GPXenergy/gpx_connector/gpx_connector/http_pages.cpp

#include <WebServer.h>
#include "http_pages.h"
#include "user_config.h"

#define TITLE_HOME "Home"
#define TITLE_UPDATE "Update firmware"
#define TITLE_STATUS "Status"
#define TITLE_CONF_DEVICE "Configure device"
#define TITLE_CONF_CONNECTION "Configure connection"

const char* success_message = "<p><em>Configurations saved!</em></p>";

const char* local_resources =
    "<link rel='stylesheet' href='/pure.css'>";

const char* online_resources =
    "<script src='https://ajax.googleapis.com/ajax/libs/jquery/3.2.1/jquery.min.js'></script>"
    "<link rel='stylesheet' href='https://use.fontawesome.com/releases/v5.8.2/css/all.css' "
    "integrity='sha384-oS3vJWv+0UjzBfQzYUhtDYW+Pj2yciDJxpsK1OYPAYjqT085Qq/1cq5FLXAZQ7Ay' crossorigin='anonymous'>";

const char* fallback_resources =
    "";

const char* update_firmware_script =
    "(e=>{const t=(...t)=>e.querySelector(...t),n=t('form'),a=t('#status');n.addEventListener('submit',e=>{e.prevent"
    "Default();const s=new FormData(n),o=t('#file').files[0],d=new XMLHttpRequest;o?(n.classList.add('uploading'),s."
    "append('update',o),d.addEventListener('load',e=>{a.innerText='Applying update...';setTimeout(()=>{a.innerText='"
    "Upload success! The device will restart to apply the update, you can change back to active mode afterwards.';co"
    "nst t=new XMLHttpRequest;t.open('get','/reboot'),t.send()},2000)}),d.addEventListener('error',e=>{a.innerText='"
    "Upload failed... Try again or contact help@gpx.nl',n.classList.remove('uploading')}),d.addEventListener('abort'"
    ",e=>{a.innerText='Upload cancelled...'}),d.upload.addEventListener('progress',e=>{if(e.lengthComputable){a.inne"
    "rText='Uploading new firmware... This can take up to 10 minutes.';const n=Math.round(e.loaded/e.total*100)+'%';"
    "t('#prg').innerText=n,t('#bar').style.width=n}}),d.open(n.method,n.action),d.send(s)):a.innerText='Please selec"
    "t a file...'})})(this.document);";

/**
 * page format
 * %s - page name (page title)
 * %d - device id (page title)
 * %s - remote resources
 * %s - local resources
 * %d - device id (menu title)
 * %s - page content (main content)
 */
const char* base_page_format_begin =
    "<!DOCTYPE html>"
    "<html lang='en'><head>"
    "<meta name='viewport' content='width=device-width, initial-scale=1.0'>"
    "<title>%s | GPX-Connector</title>"
    "%s"
    "%s"
    "<style>"
    "i{width: 25px;text-align: center;}"
    ".pure-form-message{font-style: italic;margin-bottom: 12px;}"
    "#layout{max-width: 680px;margin: auto;}"
    "#main{padding:1em;}"
    "input[type='text'],input[type='number']{max-width: 300px;width: 100%%;}"
    ".pure-menu-link{padding: 1em .7em;}"
    "</style>"
    "</head>"
    "<body>"
    "<div id='layout'>"
    "<div id='header'>"
    "<div class='pure-menu pure-menu-horizontal'>"
    "<a href='/' class='pure-menu-heading'>GPX-Connector</a>"
    "<ul class='pure-menu-list'>"
    "<li class='pure-menu-item pure-menu-has-children pure-menu-allow-hover'>"
    "<a href='#' id='menuLink1' class='pure-menu-link'><i class='fa fa-cog'></i>Configure</a>"
    "<ul class='pure-menu-children'>"
    "<li class='pure-menu-item'><a href='/device' class='pure-menu-link'><i class='fa fa-tablet'></i>Device</a></li>"
    "<li class='pure-menu-item'><a href='/connection' class='pure-menu-link'><i class='fa fa-wifi'></i>Connection</a></li>"
    "</ul></li>"
    "<li class='pure-menu-item'><a href='/update' class='pure-menu-link'><i class='fa fa-download'></i>Update firmware</a></li>"
    "<!--<li class='pure-menu-item'><a href='/status' class='pure-menu-link'><i class='fas fa-info-circle'></i>Status</a></li>-->"  // TODO: comment this out once status page is done
    "<li class='pure-menu-item'><a target='_blank' href='https://github.com/GPXenergy/gpx_connector' class='pure-menu-link'><i class='fab fa-github'></i>Github</a></li>"
    "</ul>"
    "</div>"
    "</div>"
    "<script>"
    "document.querySelectorAll('.pure-menu-item').forEach((e)=>e.children[0].href===window.location.href?e.classList.add('pure-menu-selected'):0);"
    "</script>"
    "<div id='main'>";

const char* base_page_format_end =
    "</div>"
    "</div>"
    "</body></html>";

const char* HttpPages::get_home_page() {
  return render_full_page(
      TITLE_HOME,
      "<h1>Manage your GPX-Connector</h1>"
      "<p class='pure-form-message'>GPX-Connector version %s</p>"
      "<p>"
      "<ul>"
      "<li><a href='/device'>Configure your device</a></li>"
      "<li><a href='/connection'>Configure your connection to the API</a></li>"
      "<li><a href='/update'>Update the firmware</a></li>"
      "</ul>"
      "More information about configurations in the <a href='dashboard.gpx.nl/manual' target='_blank'>User manual</a>."
      "</p>",
      GPX_CONN_VERSION
  );
}

const char* HttpPages::get_update_page() {
  return render_full_page(
      TITLE_UPDATE,
      "<div id='update'>"
      "<form class='pure-form pure-form-stacked' method='POST' enctype='multipart/form-data'>"
      "<fieldset>"
      "<legend><a href='/'>Home</a> / Update the firmware</legend>"
      "<div id='upload-inputs'>"
      "<p><em>Current version: v" GPX_CONN_VERSION "</em></p>"
      "<input type='file' name='update' id='file'><br>"
      "<span class='pure-form-message'>The latest firmware can be downloaded from <a target='_blank' href='https://github.com/GPXenergy/gpx_connector'>Github</a>. "
      "</span>"
      ""
      "<br>"
      "<input type='submit' class='pure-button pure-button-primary' value='Upload'>"
      "</div>"
      "<p id='status'></p>"
      "<div id='upload-progress'>"
      "<div style='background:#eee'><div id='bar' style='background:#ccc;height:10px'></div></div>"
      "<div id='prg' style='text-align:center'></div>"
      "</div>"
      "</fieldset>"
      "</form>"
      "<script>"
      "%s"
      "</script>"
      "<style>"
      "#upload-progress{display:none}"
      "form.uploading #upload-inputs{display:none}"
      "form.uploading #upload-progress{display:block}"
      "</style>"
      "</div>",
      update_firmware_script
  );
}

const char* HttpPages::get_config_device_page(
    bool display_success,
    const char* device_ssid,
    const char* device_password,
    uint32_t meter_conn_baud,
    uint16_t meter_conn_parity,
    bool inverter_enabled,
    uint8_t current_sensor_amps,
    uint8_t phase_type
) {
  return render_full_page(
      TITLE_CONF_DEVICE,
      "<form class='pure-form pure-form-stacked' action='/save?next=/device' method='POST'>"
      "<fieldset>"
      "<legend><a href='/'>Home</a> / Device settings</legend>"

      // GPX-Connector access point ssid
      "<label for='" FORM_NAME_AP_SSID "'>GPX-Connector wifi name</label>"
      "<input type='text' name='" FORM_NAME_AP_SSID "' id='" FORM_NAME_AP_SSID "' value='%s'>"
      "<span class='pure-form-message'>"
      "Network name for connecting to the configuration server"
      "</span>"

      // GPX-Connector access point password
      "<label for='" FORM_NAME_AP_PASS "'>GPX-Connector wifi password</label>"
      "<input type='text' name='" FORM_NAME_AP_PASS "' id='" FORM_NAME_AP_PASS "' value='%s'>"
      "<span class='pure-form-message'>"
      "Password for the configuration WiFi network (either empty or at least 8 characters long)"
      "</span>"

      "<h2>Smart meter settings</h2>"

      // GPX-Connector meter connection baud rate
      "<label for='" FORM_NAME_METER_BAUD "'>Smart meter baud rate</label>"
      "<select name='" FORM_NAME_METER_BAUD "' id='" FORM_NAME_METER_BAUD "'>"
      "<option %s value='9600'>9600</option>"
      "<option %s value='115200'>115200</option>"
      "</select>"
      "<span class='pure-form-message'>"
      "See user manual for more information."
      "</span>"

      // GPX-Connector meter connection parity
      "<label for='" FORM_NAME_METER_PARITY "'>Smart meter parity</label>"
      "<select name='" FORM_NAME_METER_PARITY "' id='" FORM_NAME_METER_PARITY "'>"
      "<option %s value='0'>7E1</option>"
      "<option %s value='1'>8N1</option>"
      "</select>"
      "<span class='pure-form-message'>"
      "See user manual for more information."
      "</span>"

      "<h2>Solar Inverter settings</h2>"

      // GPX-Connector inverter connection enabled
      "<label>Connection</label>"
      "<label for='" FORM_NAME_INVERTER_ENABLED "0' class='pure-radio'>"
      "<input id='" FORM_NAME_INVERTER_ENABLED "0' type='radio' name='" FORM_NAME_INVERTER_ENABLED "' value='0' %s>No solar inverter connected"
      "</label>"
      "<label for='" FORM_NAME_INVERTER_ENABLED "1' class='pure-radio'>"
      "<input id='" FORM_NAME_INVERTER_ENABLED "1' type='radio' name='" FORM_NAME_INVERTER_ENABLED "' value='1' %s>Connected through current sensor"
      "</label>"
      "<span class='pure-form-message'>"
      "Solar inverter is not fully supported yet, enable at own risk."
      "</span>"

      // GPX-Connector current sensor type
      "<label for='" FORM_NAME_CURRENT_SENSOR_AMPS "'>Current sensor amps per 1v</label>"
      "<select name='" FORM_NAME_CURRENT_SENSOR_AMPS "' id='" FORM_NAME_CURRENT_SENSOR_AMPS "'>"
      "<option %s value='30'>30A/1v</option>"
      "<option %s value='50'>50A/1v</option>"
      "</select>"
      "<span class='pure-form-message'>"
      "See user manual for more information."
      "</span>"

      // GPX-Connector phase type
      "<label for='" FORM_NAME_PHASE_TYPE "'>Phase type (where current sensor is connected)</label>"
      "<select name='" FORM_NAME_PHASE_TYPE "' id='" FORM_NAME_PHASE_TYPE "'>"
      "<option %s value='1'>1-phase power</option>"
      "<option %s value='3'>3-phase power</option>"
      "</select>"
      "<span class='pure-form-message'>"
      "See user manual for more information."
      "</span>"

      "<br>"
      "<button type='submit' class='pure-button pure-button-primary'>Save</button>"
      "</fieldset>"
      "</form>"
      "%s", // Success message
      device_ssid,
      device_password,
      meter_conn_baud == 9800 ? "selected" : "",
      meter_conn_baud == 115200 ? "selected" : "",
      meter_conn_parity == MeterParity::e_meter_parity_7E1 ? "selected" : "",
      meter_conn_parity == MeterParity::e_meter_parity_8N1 ? "selected" : "",
      inverter_enabled ? "" : "checked",
      inverter_enabled ? "checked" : "",
      current_sensor_amps == 30 ? "selected" : "",
      current_sensor_amps == 50 ? "selected" : "",
      phase_type == 1 ? "selected" : "",
      phase_type == 3 ? "selected" : "",
      display_success ? success_message : ""
  );
}

const char* HttpPages::get_config_connection_page(
    bool display_success,
    const char* wifi_ssid,
    const char* wifi_password,
    const char* api_key,
    bool use_dev
) {
  return render_full_page(
      TITLE_CONF_CONNECTION,
      "<form class='pure-form pure-form-stacked' action='/save?next=/connection' method='POST'>"
      "<fieldset>"
      "<legend><a href='/'>Home</a> / Connection settings</legend>"

      // WiFi ssid
      "<label for='" FORM_NAME_WIFI_SSID "'>WiFi network name</label>"
      "<input type='text' name='" FORM_NAME_WIFI_SSID "' id='" FORM_NAME_WIFI_SSID "' value='%s'>"
      "<span class='pure-form-message'>Your home WiFi network name</span>"

      // WiFi password
      "<label for='" FORM_NAME_WIFI_PASS "'>WiFi password</label>"
      "<input type='text' name='" FORM_NAME_WIFI_PASS "' id='" FORM_NAME_WIFI_PASS "' value='%s'>"
      "<span class='pure-form-message'>Your home WiFi network password</span>"

      // Api key
      "<label for='" FORM_NAME_API_KEY "'>API key</label>"
      "<input type='text' name='" FORM_NAME_API_KEY "' id='" FORM_NAME_API_KEY "' value='%s'>"
      "<span class='pure-form-message'>"
      "Get your API key from <a target='_blank' href='https://dashboard.gpx.nl/configure/meter'>dashboard.gpx.nl</a><br>"
      "</span>"

      // Use dev
      "<label>Server</label>"
      "<label for='" FORM_NAME_USE_DEV "0' class='pure-radio'>"
      "<input id='" FORM_NAME_USE_DEV "0' type='radio' name='" FORM_NAME_USE_DEV "' value='0' %s>Standard"
      "</label>"
      "<label for='" FORM_NAME_USE_DEV "1' class='pure-radio'>"
      "<input id='" FORM_NAME_USE_DEV "1' type='radio' name='" FORM_NAME_USE_DEV "' value='1' %s>Development"
      "</label>"
      "<span class='pure-form-message'>"
      "Use development for testing and development purposes, the development server will not store data."
      "</span>"

      "<br>"
      "<button type='submit' class='pure-button pure-button-primary'>Save</button>"
      "</fieldset>"
      "</form>"
      "%s",
      wifi_ssid,
      wifi_password,
      api_key,
      use_dev ? "" : "checked",
      use_dev ? "checked" : "",
      display_success ? success_message : ""
  );
}

const char* HttpPages::get_status_page() {
  return render_full_page(
      TITLE_STATUS,
      "<form class='pure-form'>"
      "<fieldset>"
      "<legend><a href='/'>Home</a> / Status</legend>"
      "<pre style='background-color:#eee;padding:5px;font-size:12px;max-width:680px'>"
      "GPX version %s [%s]<br>"
      " - Current mode: %s<br>"
      "Meter data [%s]<br>"
      " - Last data: %s<br>"
      " - Valid: %s<br>"
      "Configuration server [%s]<br>"
      " - Status: %s<br>"
      "Api connection [%s]<br>"
      " - Status: %s<br>"
      "Server connection<br>"
      " - Status: %s (%d)<br>"
      "</pre>"
      "</fieldset>"
      "</form>",
      GPX_CONN_VERSION,
      "Active", // System state
      "Fixed", // - System mode
      "Active", // status
      "...", // - meter data
      "...", // - meter datavalid
      "Active", // Server state
      "Connected with wifi", // - Server status
      "Active", // Api state
      "Data posted", // - Api status
      "OK",   // - Server status
      200
  );
}

const char* HttpPages::render_full_page(const char* page_name, const char* content_format, ...) {
  sprintf(
      transmission_buffer,
      base_page_format_begin,
      page_name,
      local_resources,
      internet_access ? online_resources : fallback_resources
  );

  va_list args;
  va_start(args, content_format);
  vsprintf(
      &transmission_buffer[strlen(transmission_buffer)],
      content_format,
      args
  );
  va_end(args);

  sprintf(
      &transmission_buffer[strlen(transmission_buffer)],
      base_page_format_end
  );

  return transmission_buffer;
}

char HttpPages::transmission_buffer[] = "";

const char* HttpPages::pure_js =
    "(function (w,d){const a='active',l=d.getElementById('layout'),m=d.getElementById('menu'),n=d"
    ".getElementById('menuLink'),c=d.getElementById('main'),tc=(e,b)=>{const r=e.className.split("
    "/\\s+/),p=r.length;let i=0;while (i < p){if(r[i]===b){r.splice(i,1);break;}i++;}if(i===p){r."
    "push(b);}e.className=r.join(' ');},ta=(e)=>{e.preventDefault();tc(l,a);tc(m,a);tc(n,a);};n.o"
    "nclick=(e)=>ta(e);c.onclick=(e)=>m.className.indexOf(a)!==-1 && ta(e);}(this,this.document));";

/**
 *
 */
bool HttpPages::internet_access = true;

/**
 * Gzipped pure css library
 * https://purecss.io/
 */
const uint8_t HttpPages::pure_css[PURE_CSS_SIZE] = {
    0x1f, 0x8b, 0x08, 0x08, 0x56, 0xa2, 0xec, 0x5c, 0x00, 0x03, 0x70, 0x75, 0x72, 0x65, 0x2d, 0x6d,
    0x69, 0x6e, 0x2e, 0x63, 0x73, 0x73, 0x00, 0xed, 0x1b, 0x6b, 0x8f, 0xe3, 0xb6, 0xf1, 0xfb, 0xfd,
    0x0a, 0xe5, 0x0e, 0x07, 0xdc, 0x1e, 0x24, 0xaf, 0x2c, 0x3f, 0x57, 0x42, 0x82, 0x26, 0xcd, 0xa5,
    0x4d, 0x91, 0x06, 0x05, 0xd2, 0x2f, 0xc5, 0x65, 0x0b, 0xd0, 0x12, 0x6d, 0xab, 0xab, 0x17, 0x24,
    0x79, 0x1f, 0xe7, 0xfa, 0xbf, 0x77, 0xf8, 0x90, 0x34, 0x7c, 0xc8, 0xf6, 0xa6, 0x45, 0xd1, 0x0f,
    0x8d, 0x73, 0x77, 0x12, 0x39, 0x1c, 0x0e, 0xe7, 0xc5, 0x99, 0x21, 0x75, 0xfb, 0xf1, 0xab, 0x37,
    0x7f, 0x39, 0xd4, 0xd4, 0x79, 0x9c, 0x4e, 0xfc, 0x89, 0xff, 0xe6, 0xf7, 0x65, 0xf5, 0x52, 0xa7,
    0xbb, 0x7d, 0xeb, 0x04, 0xfe, 0x74, 0xe6, 0xfc, 0x8d, 0xec, 0xcb, 0xf2, 0xab, 0x37, 0x3f, 0xa5,
    0x31, 0x2d, 0x1a, 0x9a, 0x38, 0x87, 0x22, 0xa1, 0xb5, 0xd3, 0xee, 0xa9, 0xf3, 0xdd, 0x2f, 0xdf,
    0x3b, 0xb2, 0x79, 0xf2, 0x66, 0xdf, 0xb6, 0x55, 0x13, 0xde, 0xde, 0xee, 0xd2, 0x76, 0x7f, 0xd8,
    0x4c, 0xe2, 0x32, 0xbf, 0x7d, 0x61, 0x23, 0x6f, 0x2b, 0x40, 0x7d, 0xbb, 0xc9, 0xca, 0xcd, 0x6d,
    0x4e, 0x9a, 0x96, 0xd6, 0xb7, 0x3f, 0xfd, 0xf8, 0xfb, 0x4f, 0x3f, 0xff, 0xf2, 0x69, 0x92, 0x27,
    0x6f, 0x3e, 0xde, 0xbe, 0xb9, 0x85, 0xd9, 0x8b, 0xb2, 0xce, 0x49, 0x96, 0x7e, 0xa1, 0x93, 0xb8,
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
    0x01, 0x01, 0x01, 0x01, 0x01, 0x01, 0x01, 0x01, 0x01, 0x01, 0x01, 0x01, 0x01, 0x01, 0x01, 0x01,
    0x01, 0x01, 0x01, 0x01, 0x01, 0x01, 0x01, 0x01, 0x01, 0x01, 0x01, 0x01, 0x01, 0x01, 0x01, 0x01,
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
};
