GPXenergy/gpx_connector/gpx_connector/configuration_server.cpp

#include <Update.h>
#include <ESPmDNS.h>
#include "configuration_server.h"
#include "user_config.h"
#include "local_storage.h"
#include "debugger.h"
#include "http_pages.h"

#define RETRY_TIMEOUT 4000

/**
 * Clamp given value between 2 other values.
 * @tparam T : return data type
 * @tparam T2 : data type of given item, will be casted to return type
 * @param val : input
 * @param min : minimum value
 * @param max : maximum value
 * @return clamped value
 */
template<typename T, typename T2>
T clamp(T2 val, T min, T max) {
  T _val = static_cast<T>(val);
  return _val < min ? min : _val > max ? max : _val;
}

ConfigWebServer::ConfigWebServer(LocalStorage& config, StatusLed& status_led)
    : Worker<bool>(false, 0),
      _server(SERVER_WIFI_PORT),
      _config(config),
      _status_led(status_led) {
}

bool ConfigWebServer::activate(bool) {
  if(WiFiConnection::wifi_connected() || WiFiConnection::ap_server_up()) {
    // Set DNS hostname for easy access
    auto hostname = _config.get_ap_ssid();
    if(MDNS.begin(hostname)) {
      WiFiConnection::set_hostname(hostname);
      MDNS.addService("http", "tcp", 80);
    }

    // Start config server
    _server.begin(SERVER_WIFI_PORT);
    return true;
  }
  return false;
}

void ConfigWebServer::deactivate() {
  _server.close();
  _server.stop();
  MDNS.end();
}

int8_t ConfigWebServer::produce_data() {
  _server.handleClient();
  if(data) {
    data = false;
    return e_worker_data_read;
  }
  return e_worker_idle;
}

void ConfigWebServer::add_urls() {
  // Home
  _server.on("/", HTTP_GET, [this]() {
    data = true;
    _server.sendHeader("Connection", "close");
    _server.send(200, "text/html", HttpPages::get_home_page());
  });

  // Configure Device
  _server.on("/device", HTTP_GET, [this]() {
    data = true;
    _server.sendHeader("Connection", "close");
    _server.send(200, "text/html", HttpPages::get_config_device_page(
        _server.hasArg("success"),
        _config.get_ap_ssid(),
        _config.get_ap_password(),
        _config.get_meter_baud(),
        _config.get_meter_parity(),
        _config.get_inverter_enabled(),
        _config.get_current_sensor_amps(),
        _config.get_phase_type()
    ));
  });

  // Configure Connection
  _server.on("/connection", HTTP_GET, [this]() {
    data = true;
    _server.sendHeader("Connection", "close");
    _server.send(200, "text/html", HttpPages::get_config_connection_page(
        _server.hasArg("success"),
        _config.get_wifi_ssid(),
        _config.get_wifi_password(),
        _config.get_api_key(),
        _config.get_use_dev()
    ));
  });

  // Save config
  _server.on("/save", HTTP_POST, [this]() {
    data = true;
    handle_save();
  });

  // Upload get
  _server.on("/update", HTTP_GET, [this]() {
    data = true;
    _server.sendHeader("Connection", "close");
    _server.send(200, "text/html", HttpPages::get_update_page());
  });

  // Status get
  _server.on("/status", HTTP_GET, [this]() {
    data = true;
    _server.sendHeader("Connection", "close");
    _server.send(200, "text/html", HttpPages::get_status_page());
  });

  // Upload post
  _server.on("/update", HTTP_POST, [this]() {
    data = true;
    // Complete
    _server.sendHeader("Connection", "close");
    if(_server.upload().totalSize == 0 || Update.hasError()) {
      _server.send(500, "text/plain", "FAIL");
    } else {
      _server.send(200, "text/plain", "OK");
    }
    _server.client().flush();
  }, [this]() {
    // Progress
    data = true;
    handle_firmware_OTA_upload();
  });

  _server.on("/reboot", [this]() { // Reboot
    _server.send(200, "text/plain", "OK");
    _server.client().flush();
    ESP.restart();
  });

  // css get
  _server.on("/pure.css", HTTP_GET, [this]() {
    _server.sendHeader("Content-Encoding", "gzip");
    _server.send_P(200, "text/css", reinterpret_cast<const char*>(HttpPages::pure_css), PURE_CSS_SIZE);
  });

  // css get
  _server.on("/favicon.ico", HTTP_GET, [this]() {
    _server.send_P(200, "image/x-icon", reinterpret_cast<const char*>(HttpPages::favicon), FAVICON_SIZE);
  });
}

void ConfigWebServer::handle_save() {
  // Get values from the form and save the new value
  if(_server.hasArg(FORM_NAME_AP_SSID)) {
    _config.set_ap_ssid(_server.arg(FORM_NAME_AP_SSID).c_str(), false);
  }
  if(_server.hasArg(FORM_NAME_AP_PASS)) {
    _config.set_ap_password(_server.arg(FORM_NAME_AP_PASS).c_str(), false);
  }
  if(_server.hasArg(FORM_NAME_WIFI_SSID)) {
    _config.set_wifi_ssid(_server.arg(FORM_NAME_WIFI_SSID).c_str(), false);
  }
  if(_server.hasArg(FORM_NAME_WIFI_PASS)) {
    _config.set_wifi_password(_server.arg(FORM_NAME_WIFI_PASS).c_str(), false);
  }
  if(_server.hasArg(FORM_NAME_API_KEY)) {
    _config.set_api_key(_server.arg(FORM_NAME_API_KEY).c_str(), false);
  }
  if(_server.hasArg(FORM_NAME_METER_BAUD)) {
    _config.set_meter_baud(_server.arg(FORM_NAME_METER_BAUD).toInt(), false);
  }
  if(_server.hasArg(FORM_NAME_METER_PARITY)) {
    _config.set_meter_parity(static_cast<MeterParity>(_server.arg(FORM_NAME_METER_PARITY).toInt()), false);
  }
  if(_server.hasArg(FORM_NAME_INVERTER_ENABLED)) {
    _config.set_inverter_enabled(_server.arg(FORM_NAME_INVERTER_ENABLED) == "1", false);
  }
  if(_server.hasArg(FORM_NAME_CURRENT_SENSOR_AMPS)) {
    _config.set_current_sensor_amps(_server.arg(FORM_NAME_CURRENT_SENSOR_AMPS).toInt(), false);
  }
  if(_server.hasArg(FORM_NAME_PHASE_TYPE)) {
    _config.set_phase_type(_server.arg(FORM_NAME_PHASE_TYPE).toInt(), false);
  }
  if(_server.hasArg(FORM_NAME_USE_DEV)) {
    _config.set_use_dev(_server.arg(FORM_NAME_USE_DEV) == "1", false);
  }

  // Redirect to same page, but now with a success message!
  _server.sendHeader("Location", _server.arg("next") + "?success=true");
  _server.send(302, "text/html");
  _server.client().flush();
}

void ConfigWebServer::handle_firmware_OTA_upload() {
  HTTPUpload& upload = _server.upload();
  switch(upload.status) {
    case UPLOAD_FILE_START: {
      DEBUG_PRINTF("Update: %s\n", upload.filename.c_str());
      if(Update.begin(UPDATE_SIZE_UNKNOWN)) {
        DEBUG_PRINTLN("Starting update");
        _status_led.set_ota_updating();
      } else {
        DEBUG_PRINTLN("Unable to start update");
      }
      break;
    }
    case UPLOAD_FILE_WRITE: {
      DEBUG_PRINTF(".");
      auto write_size = Update.write(upload.buf, upload.currentSize);
      if(write_size != upload.currentSize) {
        DEBUG_PRINTF("Something failed while uploading (wrote %d out of %d)\n", write_size, upload.currentSize);
        Update.abort();
      }
      break;
    }
    case UPLOAD_FILE_END: {
      if(upload.totalSize > 0 && Update.end(true)) { //true to set the size to the current progress
        DEBUG_PRINTF("\nUpdate Success: %u\n", upload.totalSize);
      } else {
        DEBUG_PRINTF("Update Failed...");
      }
      break;
    }
    case UPLOAD_FILE_ABORTED: {
      Update.abort();
      DEBUG_PRINTF("Update aborted...");
      break;
    }
  }
}

void ConfigWebServer::initialize() {
  add_urls();
}
